RooK-Computer/RooK-Mk3.1/STLs/LegoInspiredCase_by_Konnexus_Mk1/Case-STLs/SlotCover.stl

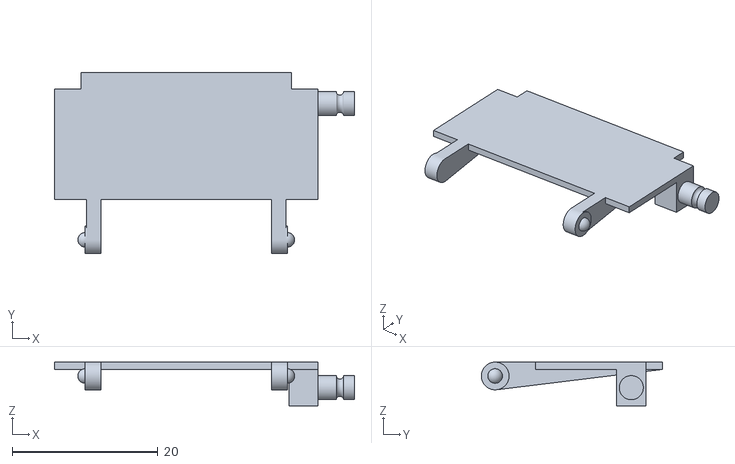
[picture p15: CAD file, 2025-12-22]
STLs/LegoInspiredCase_by_Konnexus_Mk1/Case-STLs/SlotCover.stl
41.1 x 24.8 x 6.00
