RooK-Computer/RooK-Mk3.1/STLs/LegoInspiredCase_by_Konnexus_Mk1/Case-STLs/ShutdownButton_border.stl

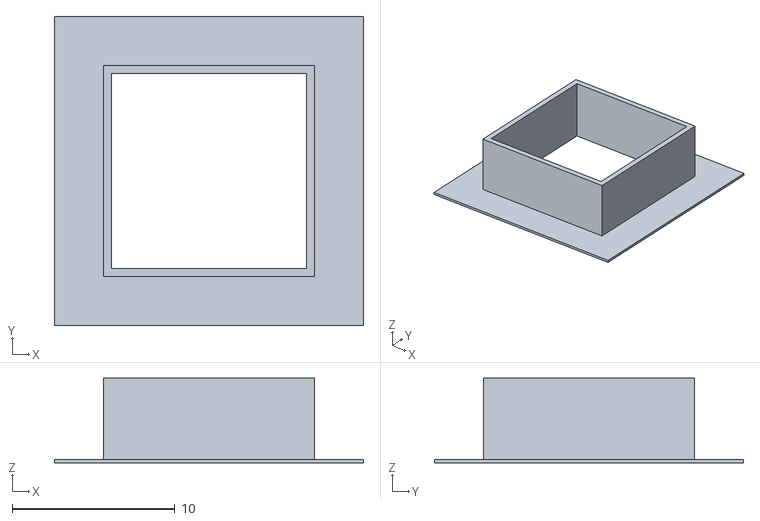
[picture p16: CAD file, 2025-12-22]
STLs/LegoInspiredCase_by_Konnexus_Mk1/Case-STLs/ShutdownButton_border.stl
19.0 x 19.0 x 5.20
