RooK-Computer/RooK-Mk3.1/STLs/LegoInspiredCase_by_Konnexus_Mk1/Case-STLs/QuitButton_fat.stl

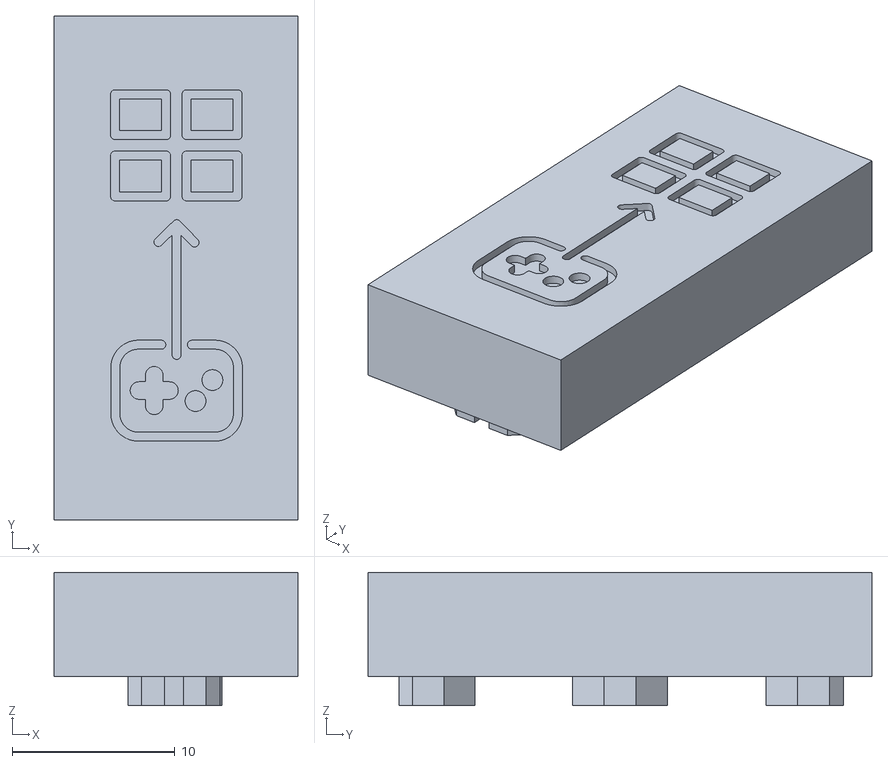
[picture p17: CAD file, 2025-12-22]
STLs/LegoInspiredCase_by_Konnexus_Mk1/Case-STLs/QuitButton_fat.stl
15.0 x 31.0 x 8.21
