RooK-Computer/RooK-Mk3.1/STLs/LegoInspiredCase_by_Konnexus_Mk1/Case-STLs/Pillars.stl

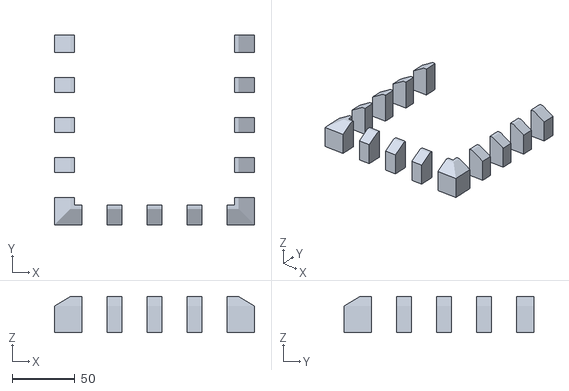
[picture p18: CAD file, 2025-12-22]
STLs/LegoInspiredCase_by_Konnexus_Mk1/Case-STLs/Pillars.stl
159.8 x 151.8 x 28.8
