RooK-Computer/RooK-Mk3.1/STLs/LegoInspiredCase_by_Konnexus_Mk1/Case-STLs/Base.stl

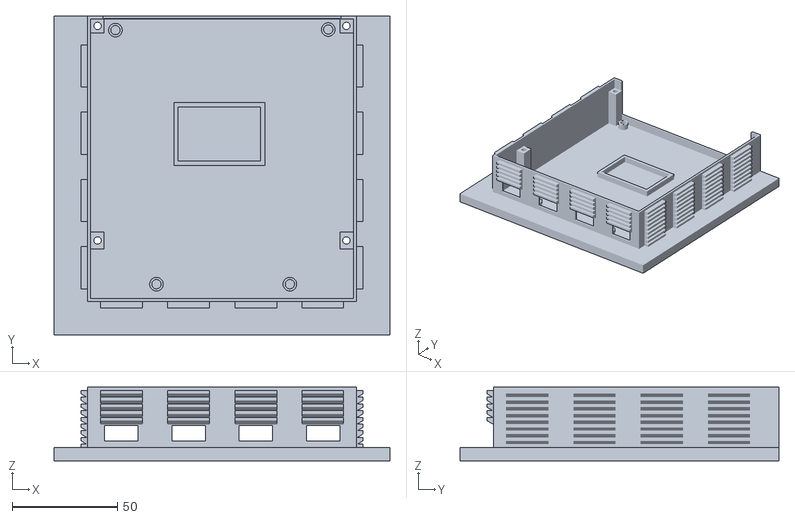
[picture p19: CAD file, 2025-12-22]
STLs/LegoInspiredCase_by_Konnexus_Mk1/Case-STLs/Base.stl
159.8 x 151.8 x 35.2
