RooK-Computer/RooK-Mk3.1/STLs/LegoInspiredCase_by_Konnexus_Mk1/Case-STLs/ResetButton_fat_print.stl

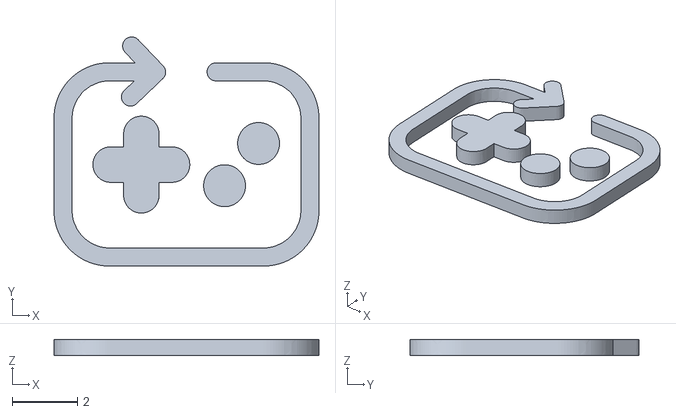
[picture p20: CAD file, 2025-12-22]
STLs/LegoInspiredCase_by_Konnexus_Mk1/Case-STLs/ResetButton_fat_print.stl
8.09 x 7.00 x 0.5
