RooK-Computer/RooK-Mk3.1/STLs/LegoInspiredCase_by_Konnexus_Mk1/Case-STLs/QuitButton_fat_border.stl

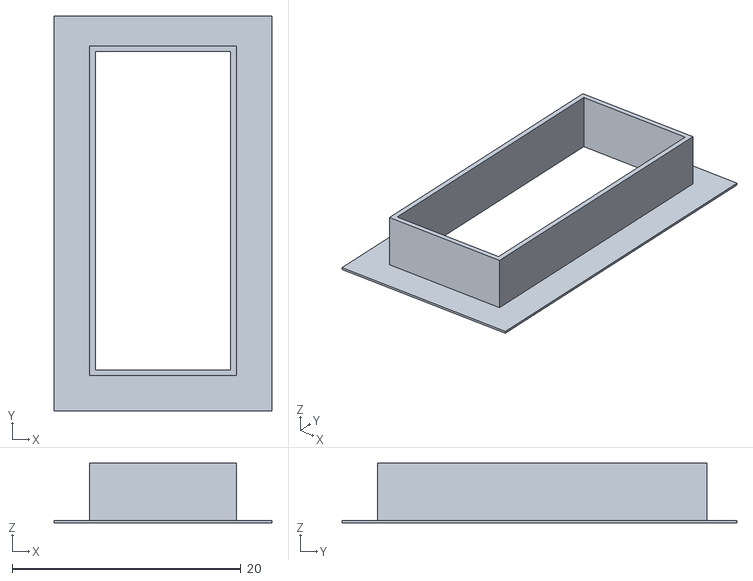
[picture p21: CAD file, 2025-09-27]
STLs/LegoInspiredCase_by_Konnexus_Mk1/Case-STLs/QuitButton_fat_border.stl
19.0 x 34.5 x 5.20
